PranitSinghSanwalka/AQeye/FirstPrototype/Photos and Videos First Prototype/Paper prototyping 2.jpeg

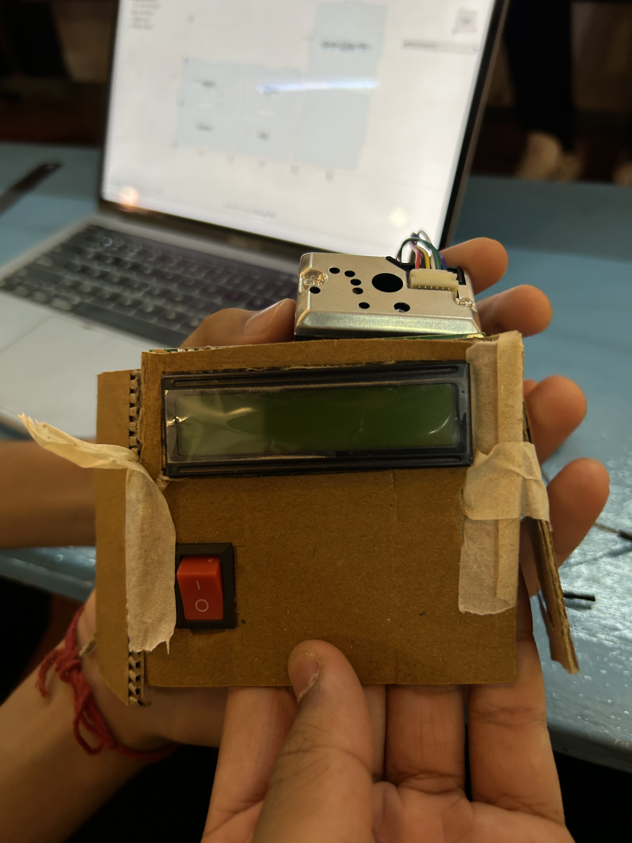
FirstPrototype/Photos and Videos First Prototype/Paper prototyping 2.jpeg
