PranitSinghSanwalka/AQeye/FirstPrototype/Photos and Videos First Prototype/Paper prototyping 3.jpeg

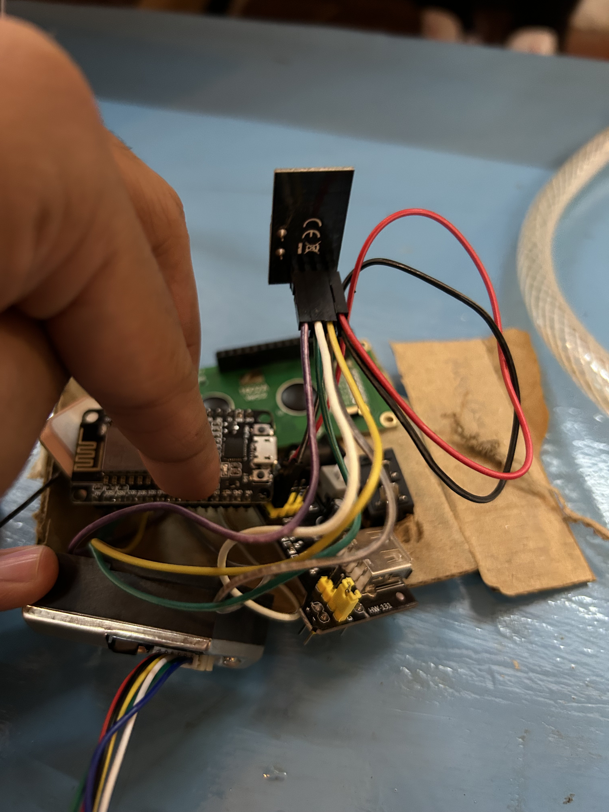
FirstPrototype/Photos and Videos First Prototype/Paper prototyping 3.jpeg
