PranitSinghSanwalka/AQeye/FirstPrototype/Photos and Videos First Prototype/Paper prototyping 4.jpeg

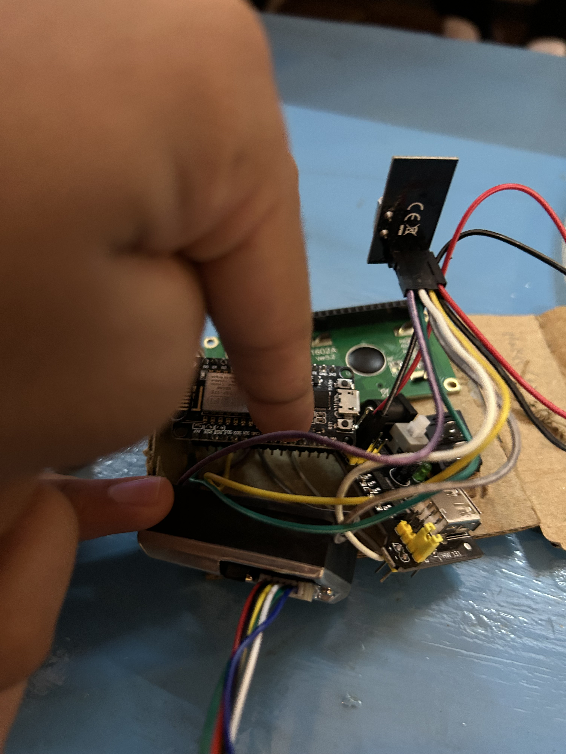
FirstPrototype/Photos and Videos First Prototype/Paper prototyping 4.jpeg
