PranitSinghSanwalka/AQeye/FirstPrototype/Photos and Videos First Prototype/Paper prototyping.jpeg

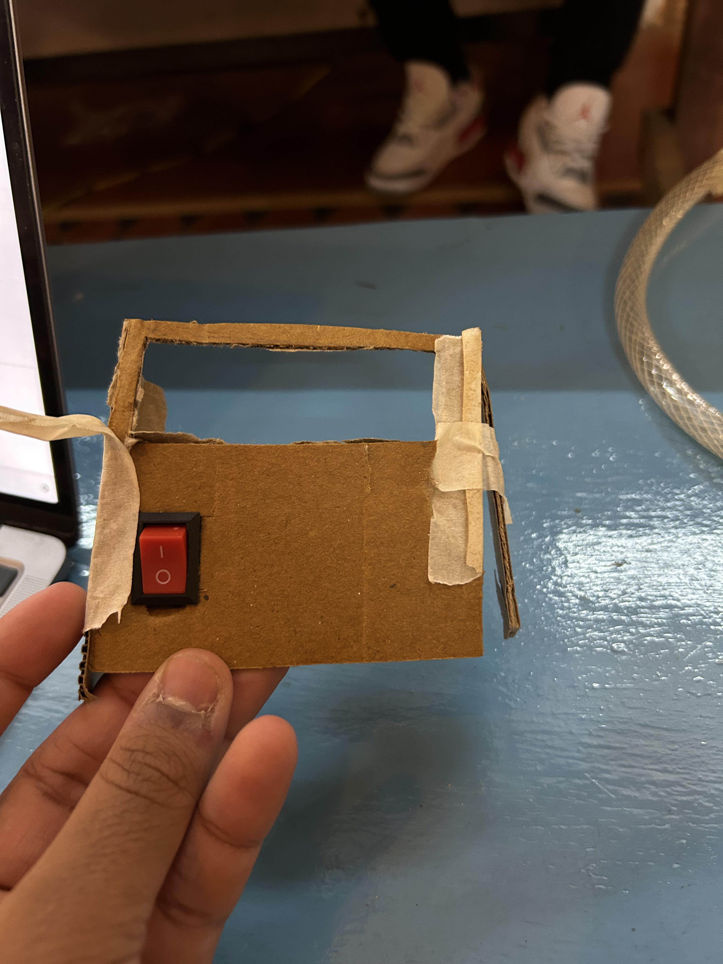
FirstPrototype/Photos and Videos First Prototype/Paper prototyping.jpeg
