PranitSinghSanwalka/AQeye/FirstPrototype/Photos and Videos First Prototype/Paper_Prototype4.jpeg

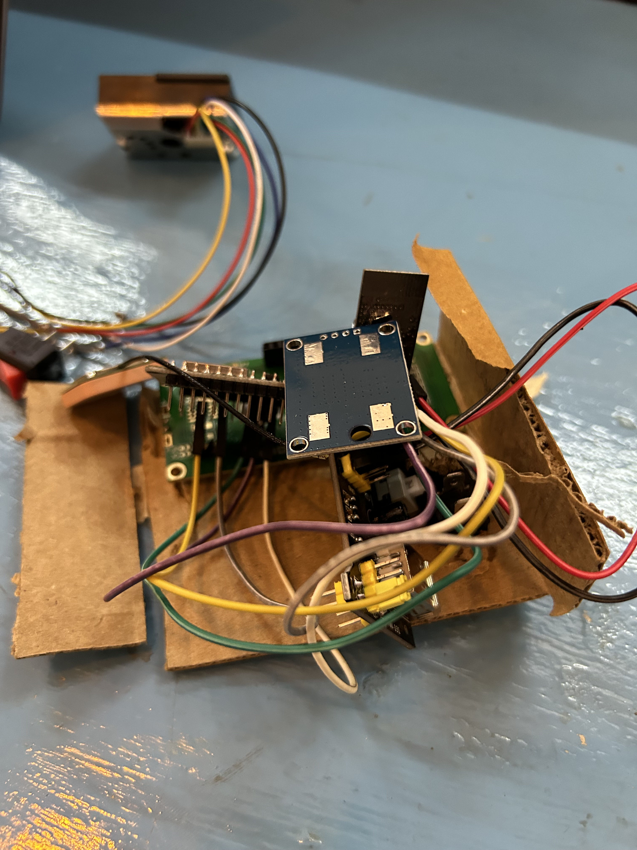
FirstPrototype/Photos and Videos First Prototype/Paper_Prototype4.jpeg
