PranitSinghSanwalka/AQeye/Second Prototype/Second Prototype Photos and Videos/Blynk_Pollutant_Readout_IOS.jpeg

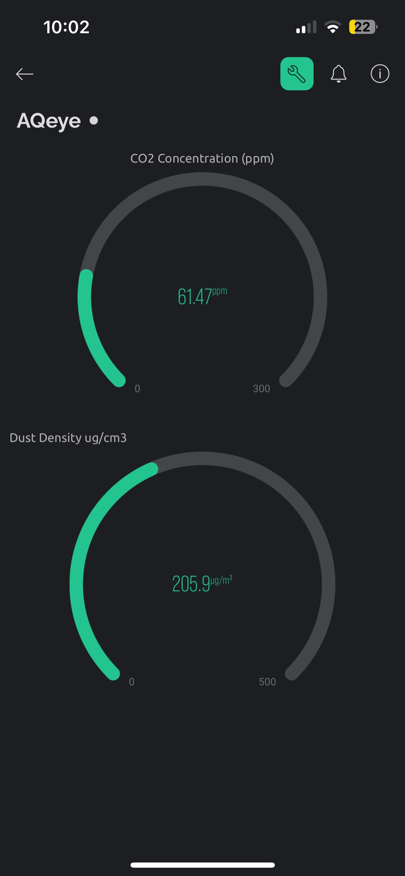
Second Prototype/Second Prototype Photos and Videos/Blynk_Pollutant_Readout_IOS.jpeg
