PranitSinghSanwalka/AQeye/Second Prototype/Second Prototype Photos and Videos/Cardboard_prototype_with_sensors.jpeg

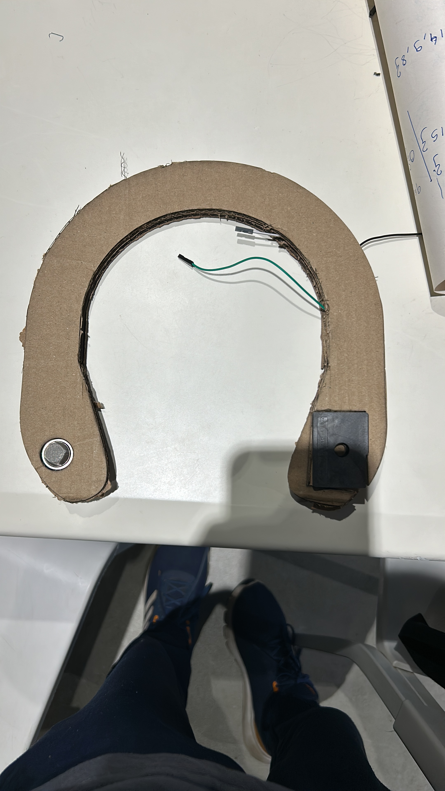
Second Prototype/Second Prototype Photos and Videos/Cardboard_prototype_with_sensors.jpeg
