PranitSinghSanwalka/AQeye/Second Prototype/Second Prototype Photos and Videos/Exploring_power_Sources.jpeg

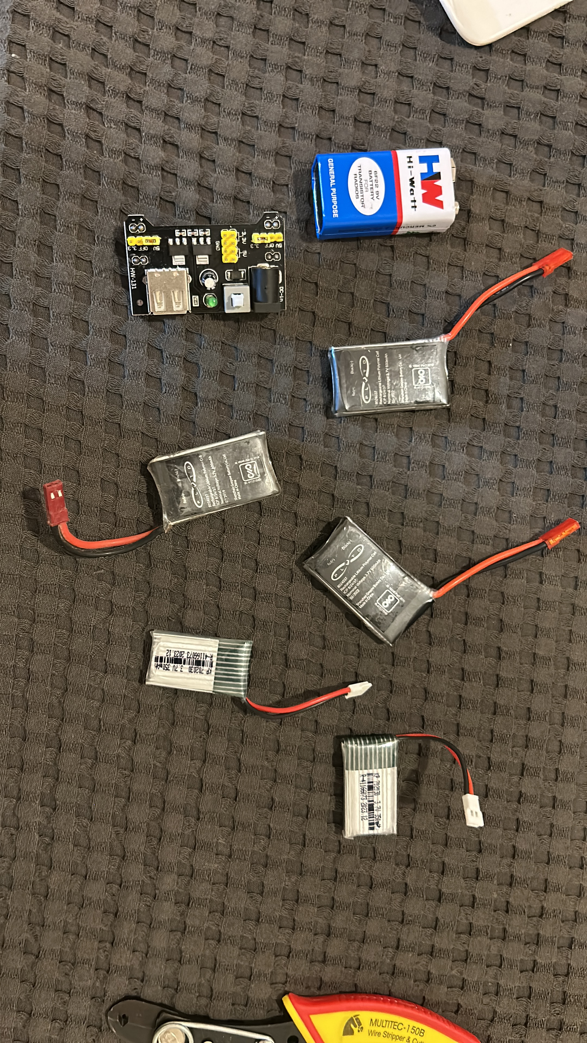
Second Prototype/Second Prototype Photos and Videos/Exploring_power_Sources.jpeg
