PranitSinghSanwalka/AQeye/Second Prototype/Second Prototype Photos and Videos/Second_prototype_closeup_side.jpeg

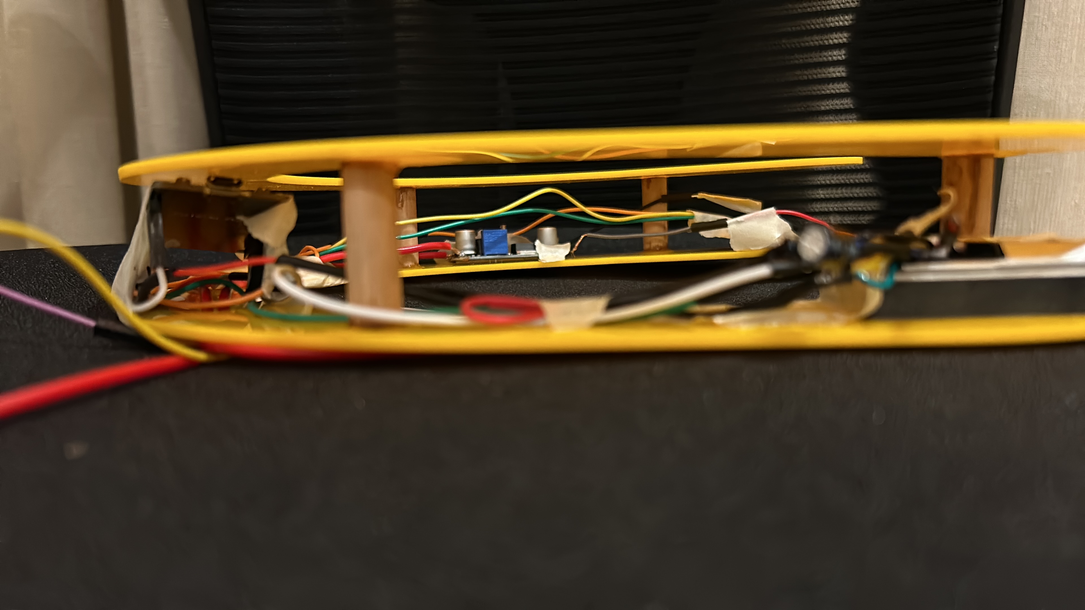
Second Prototype/Second Prototype Photos and Videos/Second_prototype_closeup_side.jpeg
