PranitSinghSanwalka/AQeye/Second Prototype/Second Prototype Photos and Videos/Wearing_second_protoype.jpeg

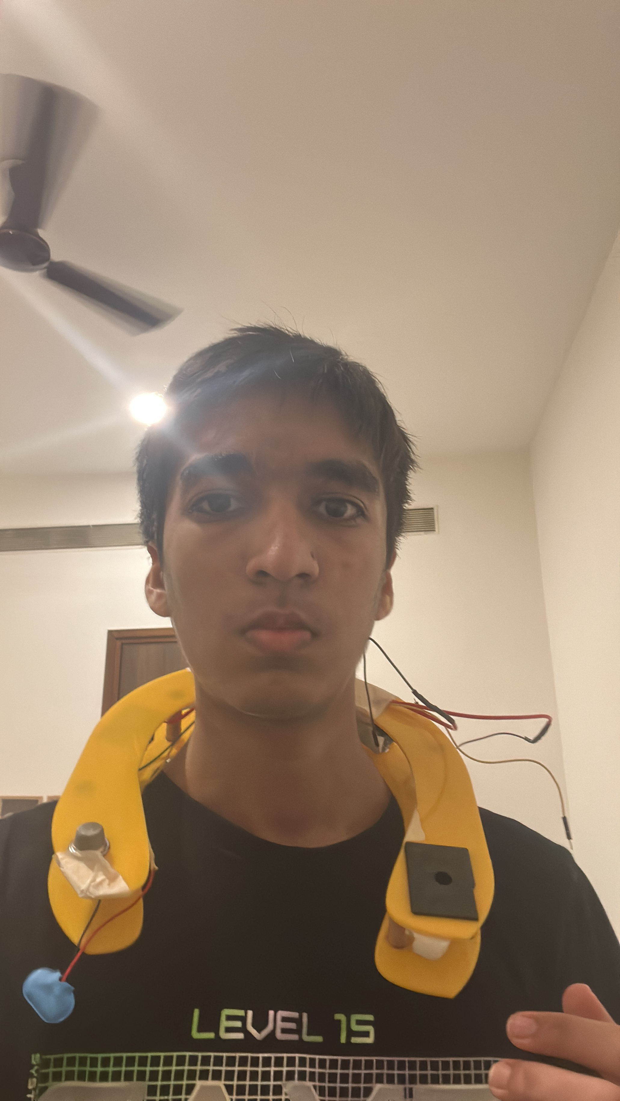
Second Prototype/Second Prototype Photos and Videos/Wearing_second_protoype.jpeg
