PranitSinghSanwalka/AQeye/FirstPrototype/Photos and Videos First Prototype/Testing_components2B.JPG

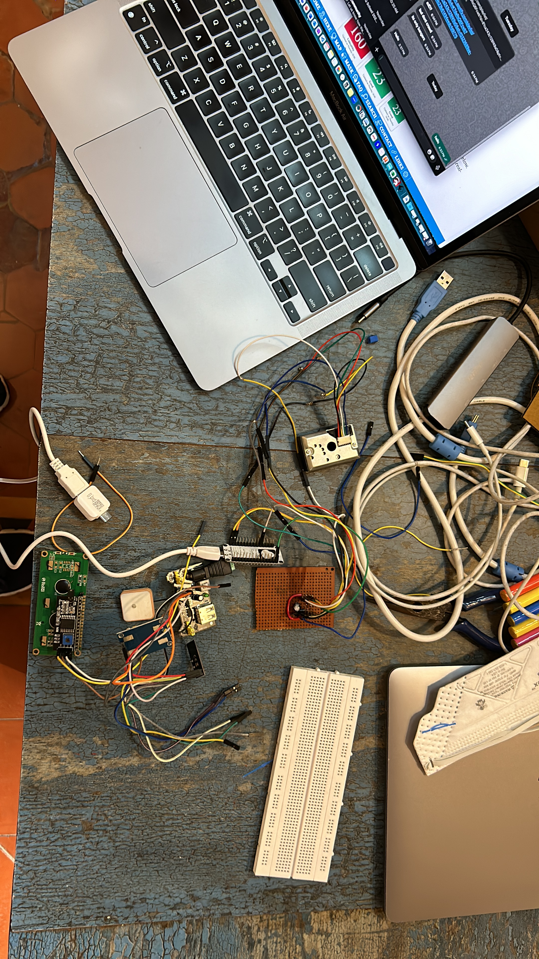
FirstPrototype/Photos and Videos First Prototype/Testing_components2B.JPG
