PranitSinghSanwalka/AQeye/Second Prototype/Second Prototype Photos and Videos/Prototype 2 with components taped_2.jpeg

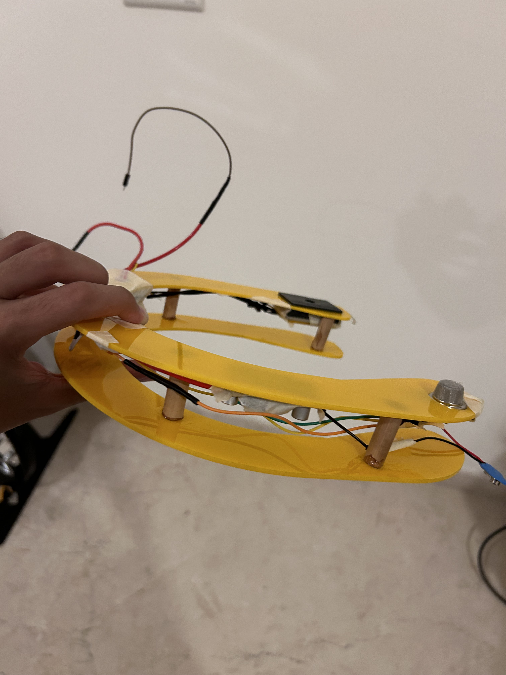
Second Prototype/Second Prototype Photos and Videos/Prototype 2 with components taped_2.jpeg
