PranitSinghSanwalka/AQeye/Second Prototype/Second Prototype Photos and Videos/Testing_Components.jpeg

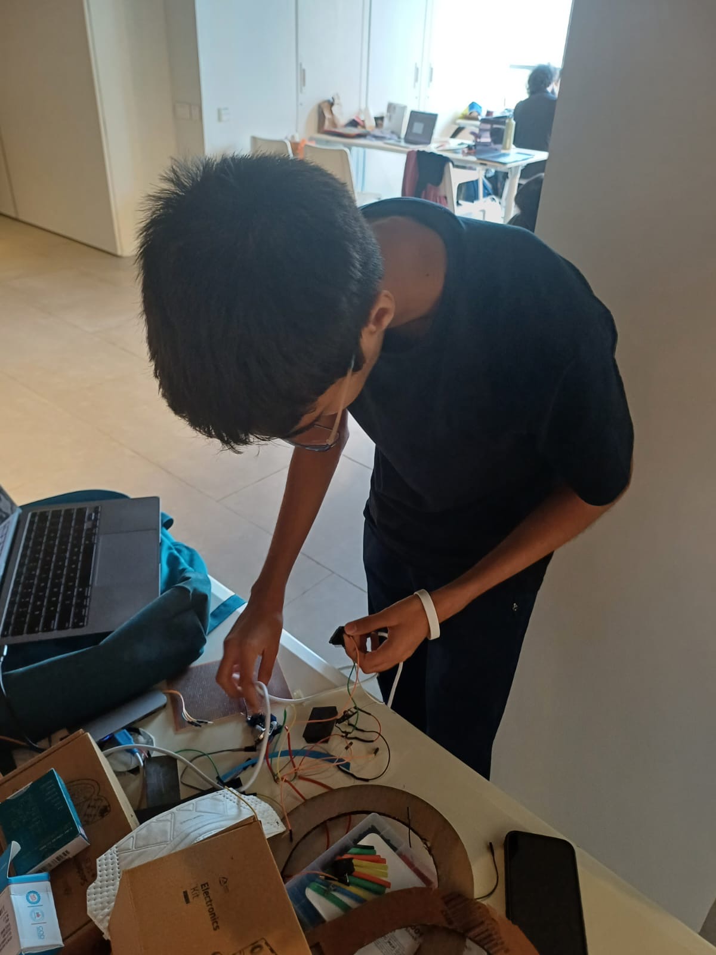
Second Prototype/Second Prototype Photos and Videos/Testing_Components.jpeg
