PranitSinghSanwalka/AQeye/FirstPrototype/Photos and Videos First Prototype/3D_Printing_Button_Fail2.jpeg

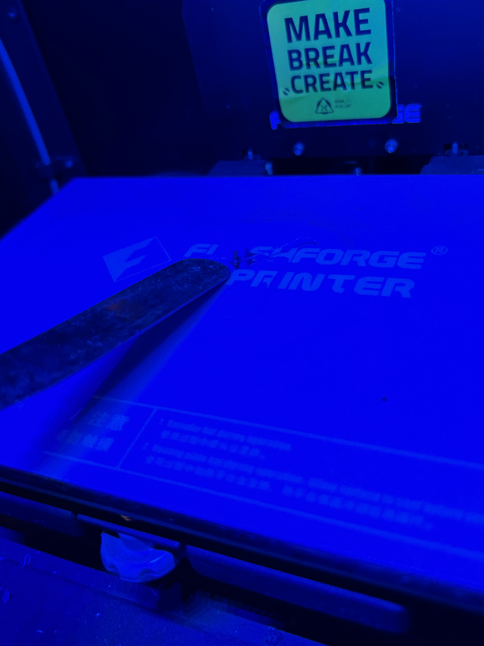
FirstPrototype/Photos and Videos First Prototype/3D_Printing_Button_Fail2.jpeg
