PranitSinghSanwalka/AQeye/FirstPrototype/Photos and Videos First Prototype/3D_Printing_Button_Fail.jpeg

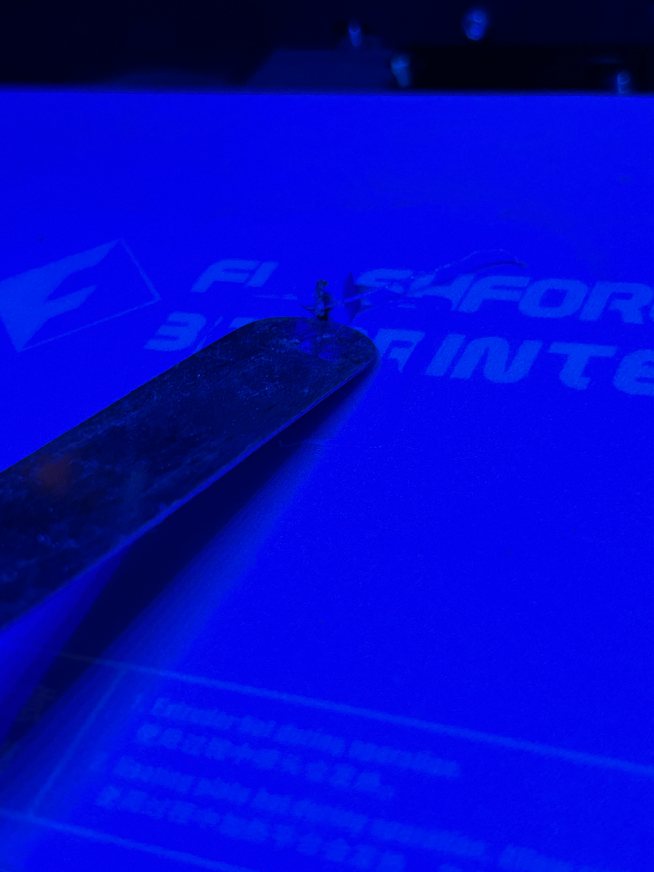
FirstPrototype/Photos and Videos First Prototype/3D_Printing_Button_Fail.jpeg
