PranitSinghSanwalka/AQeye/Second Prototype/Second Prototype Photos and Videos/Wiring_components_3.jpeg

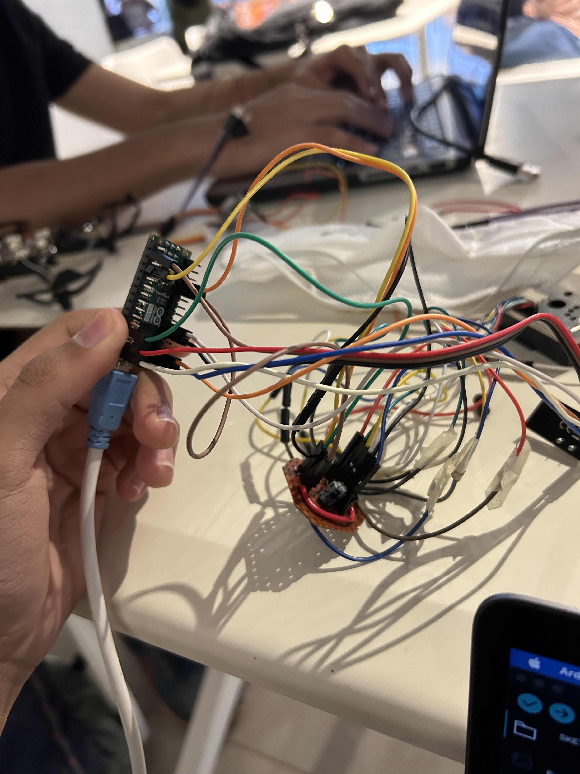
Second Prototype/Second Prototype Photos and Videos/Wiring_components_3.jpeg
