PranitSinghSanwalka/AQeye/FirstPrototype/Photos and Videos First Prototype/Paper prototype packaging testing 2.jpeg

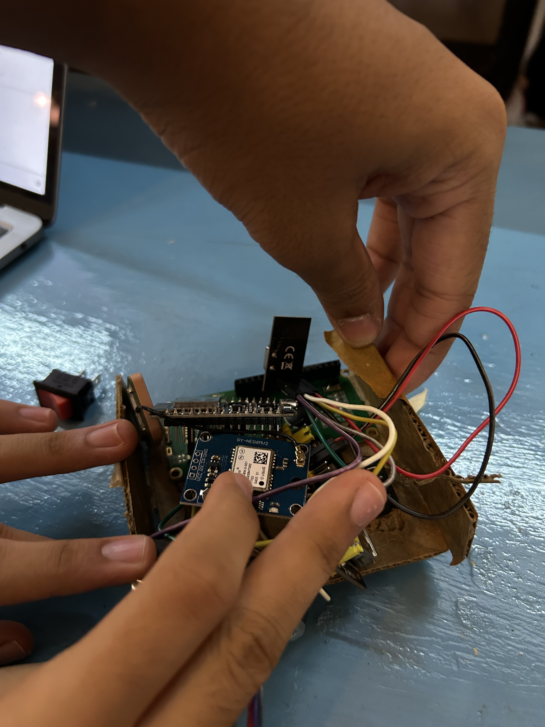
FirstPrototype/Photos and Videos First Prototype/Paper prototype packaging testing 2.jpeg
