PranitSinghSanwalka/AQeye/FirstPrototype/Photos and Videos First Prototype/Paper protytpe packaging testing.jpeg

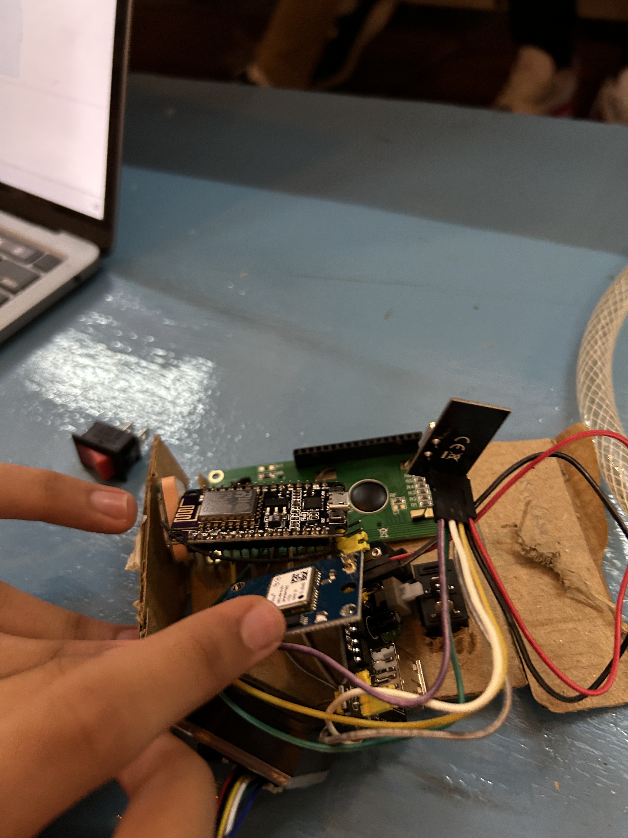
FirstPrototype/Photos and Videos First Prototype/Paper protytpe packaging testing.jpeg
