PranitSinghSanwalka/AQeye/FirstPrototype/Photos and Videos First Prototype/Testing_GPS_Module.jpeg

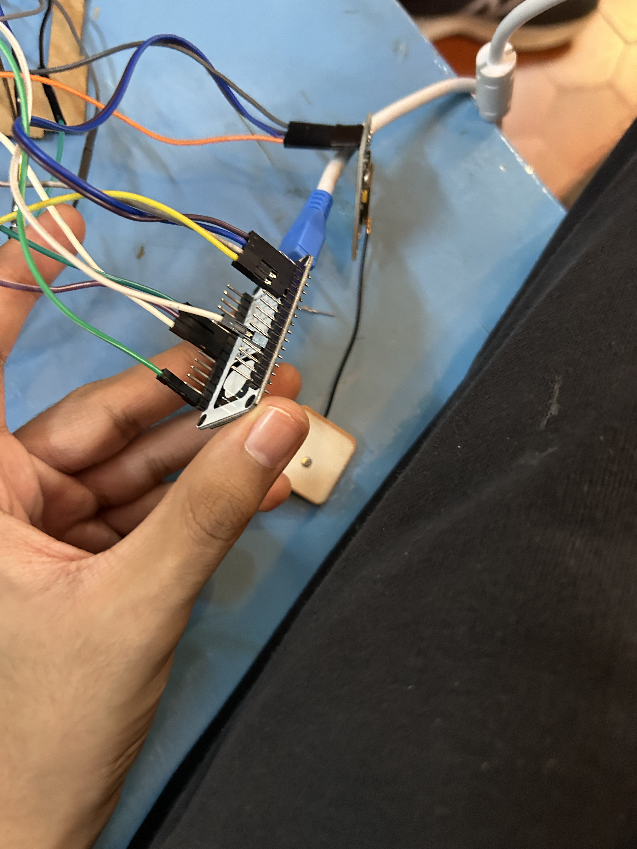
FirstPrototype/Photos and Videos First Prototype/Testing_GPS_Module.jpeg
