PranitSinghSanwalka/AQeye/FirstPrototype/Photos and Videos First Prototype/Coding_hub2.jpeg

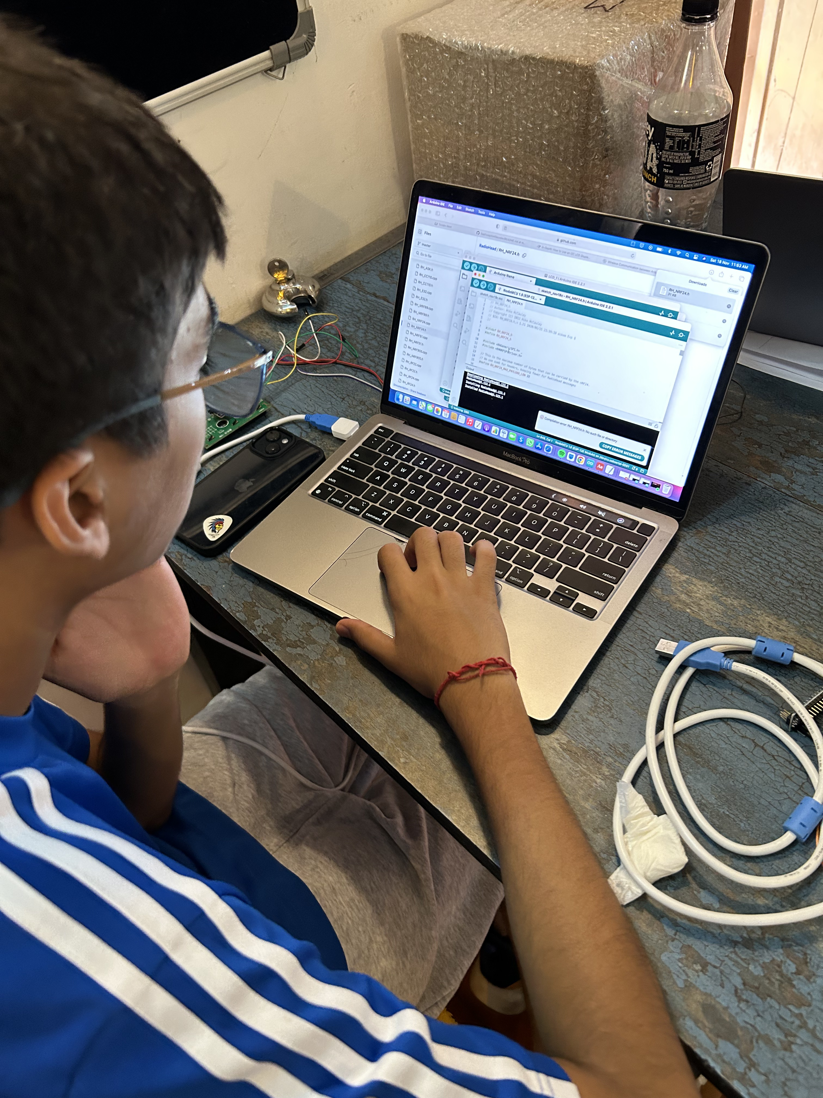
FirstPrototype/Photos and Videos First Prototype/Coding_hub2.jpeg
