PranitSinghSanwalka/AQeye/FirstPrototype/Photos and Videos First Prototype/Coding_hub.jpeg

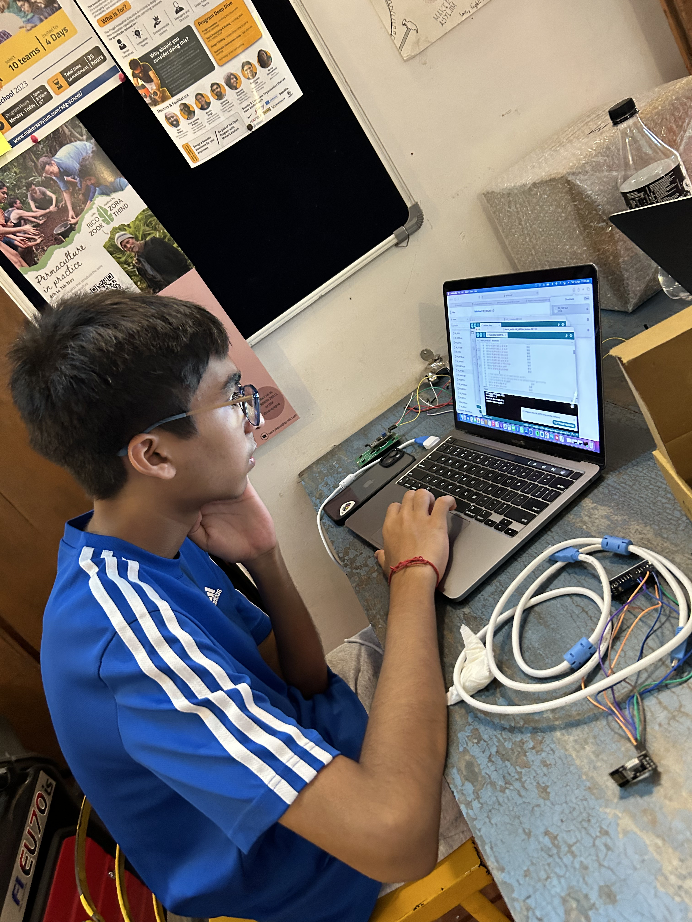
FirstPrototype/Photos and Videos First Prototype/Coding_hub.jpeg
