PranitSinghSanwalka/AQeye/FirstPrototype/Photos and Videos First Prototype/IMG_5534.jpeg

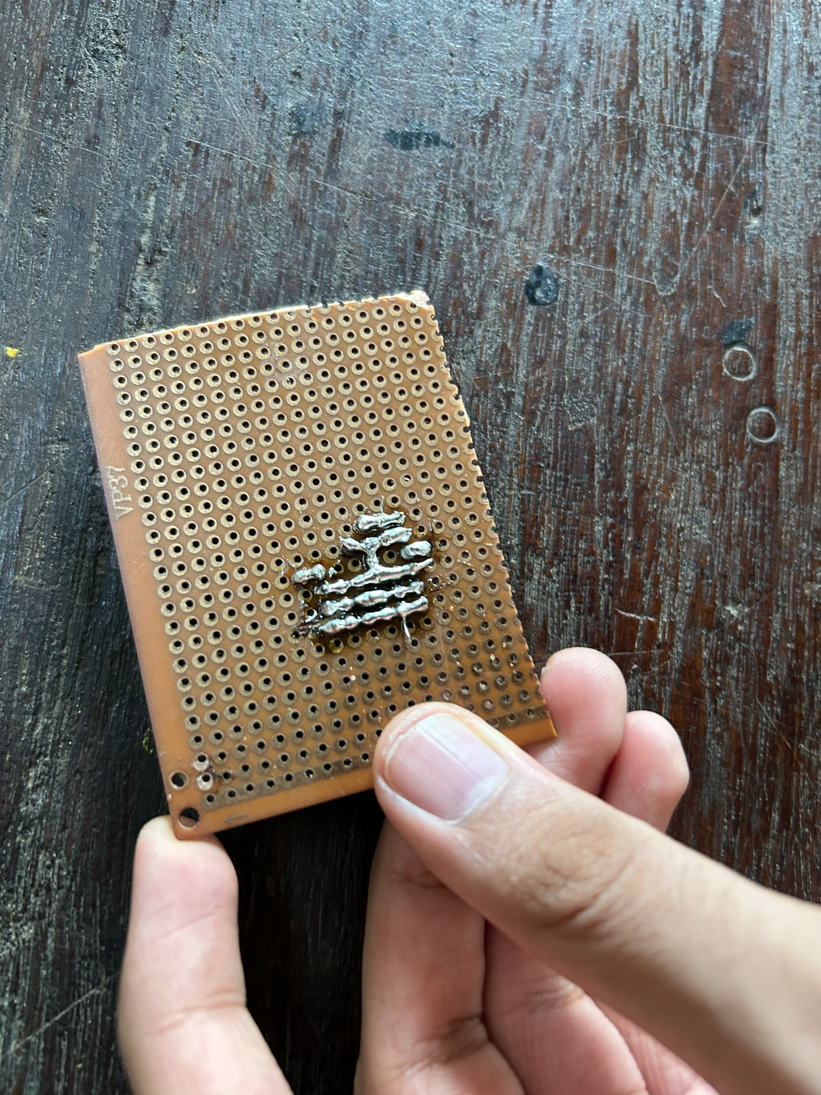
FirstPrototype/Photos and Videos First Prototype/IMG_5534.jpeg
