PranitSinghSanwalka/AQeye/FirstPrototype/Photos and Videos First Prototype/Laser cutting hub_box.jpeg

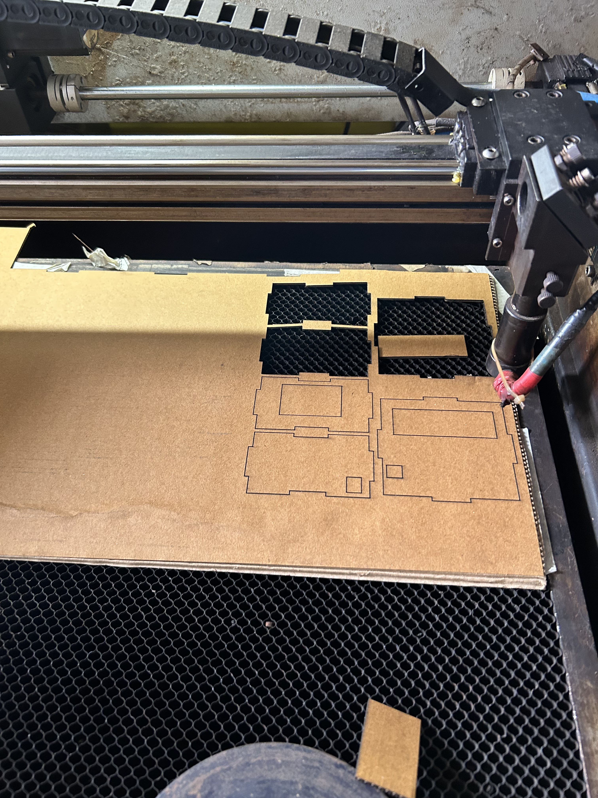
FirstPrototype/Photos and Videos First Prototype/Laser cutting hub_box.jpeg
