PranitSinghSanwalka/AQeye/FirstPrototype/Photos and Videos First Prototype/Wiring_components.jpeg

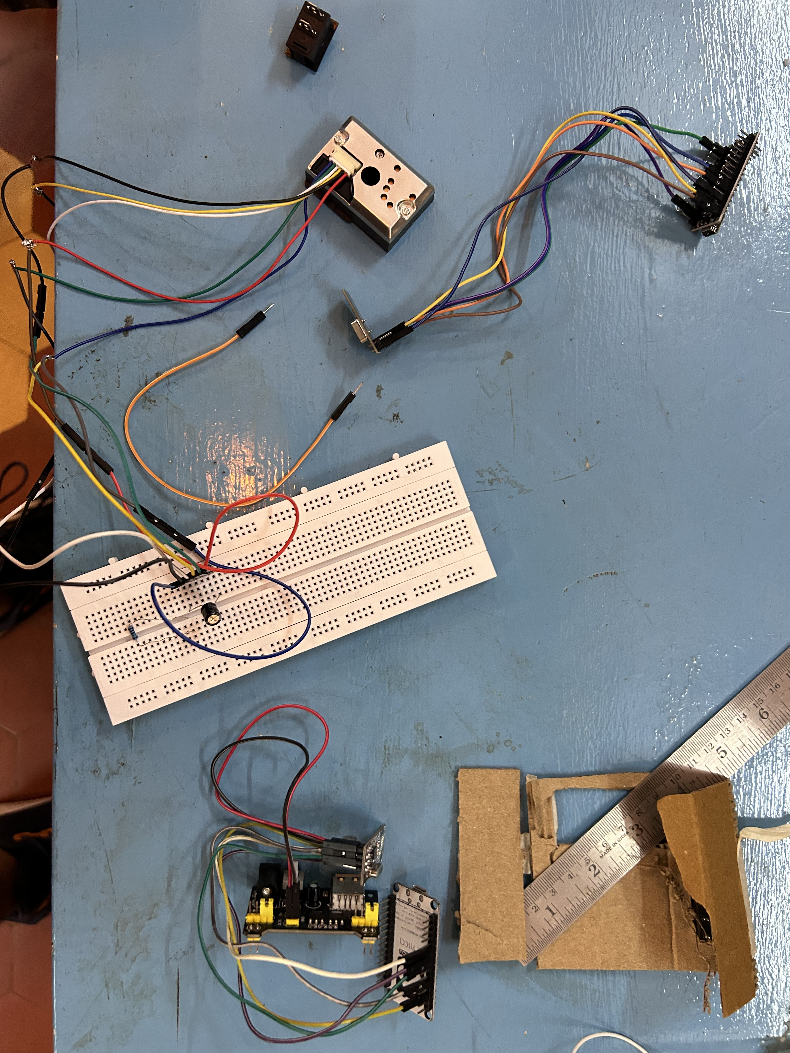
FirstPrototype/Photos and Videos First Prototype/Wiring_components.jpeg
