PranitSinghSanwalka/AQeye/Second Prototype/Second Prototype Photos and Videos/Making_prototype_2_cardboard.jpeg

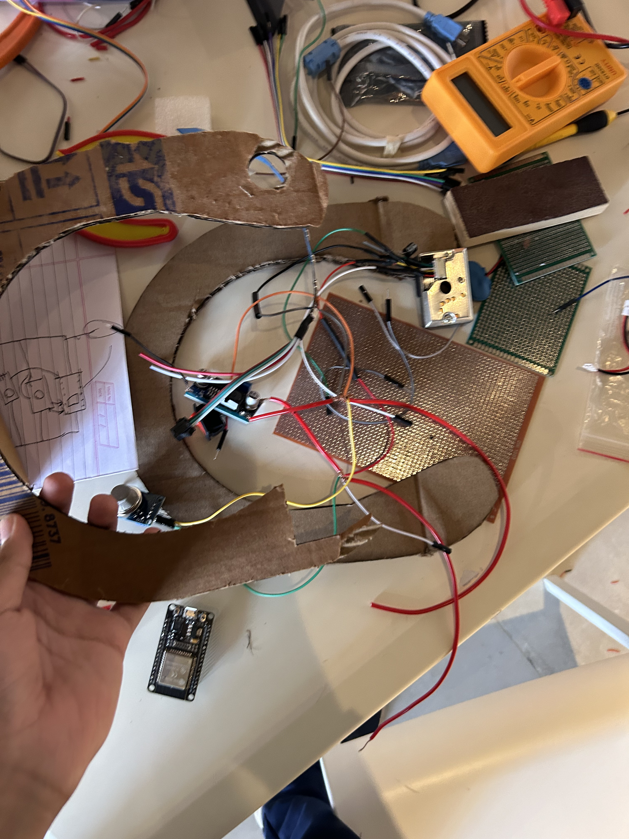
Second Prototype/Second Prototype Photos and Videos/Making_prototype_2_cardboard.jpeg
